vincentduongbruh/Intelligent-Industrial-Machine-Monitoring-/src/esp1/main/MPU9250.cpp

#include "MPU9250.h"

static constexpr float ACC_SENS = 16384.0f;

MPU9250::MPU9250(uint8_t addr): address(addr) {}

bool MPU9250::begin(int sda, int scl) {
    static bool wireInit = false;
    if (!wireInit) {
        if (sda >= 0 && scl >= 0) Wire.begin(sda, scl);
        else Wire.begin();
        wireInit = true;
    }

    Wire.beginTransmission(address);
    Wire.write(0x6B);
    Wire.write(0x00);
    if (Wire.endTransmission() != 0) return false;

    Wire.beginTransmission(address);
    Wire.write(0x1C);
    Wire.write(0x00);
    if (Wire.endTransmission() != 0) return false;

    Wire.beginTransmission(address);
    Wire.write(0x1D);
    Wire.write(0x03);
    return (Wire.endTransmission() == 0);
}

bool MPU9250::readAccelRaw(int16_t& ax, int16_t& ay, int16_t& az) {
    Wire.beginTransmission(address);
    Wire.write(0x3B);
    if (Wire.endTransmission(false) != 0) return false;

    if (Wire.requestFrom((int)address, 6) != 6) return false;

    ax = (Wire.read() << 8) | Wire.read();
    ay = (Wire.read() << 8) | Wire.read();
    az = (Wire.read() << 8) | Wire.read();

    return true;
}

bool MPU9250::readAccelG(float& ax, float& ay, float& az) {
    int16_t rx, ry, rz;
    if (!readAccelRaw(rx, ry, rz)) return false;

    ax = (rx - ax_bias) / ACC_SENS;
    ay = (ry - ay_bias) / ACC_SENS;
    az = (rz - az_bias) / ACC_SENS;

    ax = axFilter.update(ax);
    ay = ayFilter.update(ay);
    az = azFilter.update(az);

    return true;
}

void MPU9250::calibrate(int samples) {
    int32_t xs = 0, ys = 0, zs = 0;

    for (int i = 0; i < samples; i++) {
        int16_t ax, ay, az;
        if (readAccelRaw(ax, ay, az)) {
            xs += ax;
            ys += ay;
            zs += az;
        }
        delay(2);
    }

    ax_bias = xs / samples;
    ay_bias = ys / samples;
    az_bias = (zs / samples) - ACC_SENS;
}
